daskals/Soil-Moisture-Scatter-Radio-Networking-with-Low-Power/Sensor Node-Tag/Version_Relative_Humidity/Kabianaki_TwoLayer/regulated_sensorTHV18.brd

## EAGLE design Sensor Node-Tag/Version_Relative_Humidity/Kabianaki_TwoLayer/regulated_sensorTHV18.brd (2017-01-12)

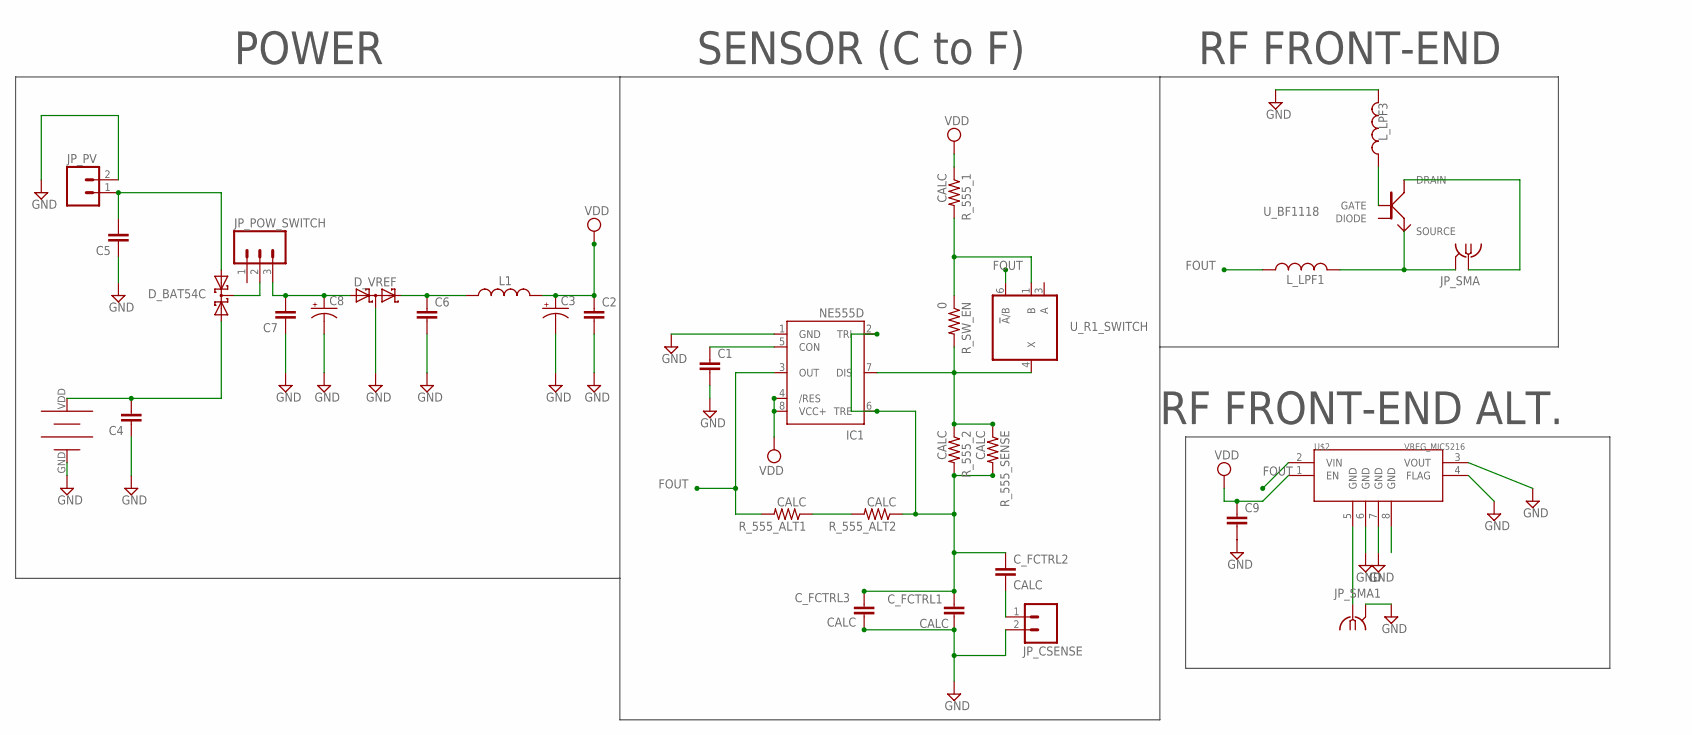
[picture p13: schematic regulated_sensorTHV18.sch]

Parts:
C1, C2, C4, C5, C6, C7, C9: CAP0603-CAP; 0603-CAP
C3, C8: CAP_POL1206; EIA3216
C_FCTRL1, C_FCTRL2, C_FCTRL3: CALC; 0603-CAP
D_BAT54C: BAT54C; SOT23
D_VREF: BAT54S; SOT23
IC1: NE555D; SO08
JP_CSENSE: M02LOCK; 1X02_LOCK
JP_POW_SWITCH: M03LOCK; 1X03_LOCK
JP_PV: M02LOCK; 1X02_LOCK
JP_SMA, JP_SMA1: SMA-142-0701-881/886; J502-ND-142-0701-881/886
L1: INDUCTOR0603; 0603
L_LPF1, L_LPF3: INDUCTOR0603; 0603
R_555_1: CALC; 0805
R_555_2, R_555_ALT1, R_555_ALT2, R_555_SENSE: CALC; 0603-RES
R_SW_EN: 0; 0805
U$1: BATTERY_AAA_EAGLE_PLASTIC_DEVICES_DOUBLE; BATTERY-AAA-50MM-DOUBLE
U$2: VREG_MIC5216; MSOP8
U_BF1118: BF1118SOT343R_NXP; SOT343R
U_R1_SWITCH: 741G3157DCKR; DCK_R-PDSO-G6

Connections:
FOUT: IC1.3 (OUT), L_LPF1.1, R_555_ALT1.2, U$2.2 (VIN), U_R1_SWITCH.6 (!A!/B)
GND: C1.2, C2.2, C3.C (-), C4.1, C5.1, C6.2, C7.1, C8.C (-), C9.2, C_FCTRL1.2, C_FCTRL3.2, D_VREF.3 (C1A2), IC1.1 (GND), JP_CSENSE.2, JP_PV.2, JP_SMA1.G@1 (2), JP_SMA1.G@2 (2), JP_SMA1.G@3 (2), JP_SMA1.G@4 (2), L_LPF3.2, U$1.GND, U$2.3 (VOUT), U$2.4 (FLAG), U$2.6 (GND), U$2.7 (GND), U_R1_SWITCH.2 (GND)
unnamed: C5.2, D_BAT54C.1 (A1), JP_PV.1
unnamed: C7.2, C8.A (+), D_VREF.1 (A1), JP_POW_SWITCH.3
unnamed: D_BAT54C.3 (CC), JP_POW_SWITCH.2
unnamed: L_LPF3.1, U_BF1118.1 (GATE)
unnamed: C6.1, D_VREF.2 (C2), L1.1
unnamed: C_FCTRL1.1, C_FCTRL2.1, C_FCTRL3.1, IC1.2 (TRI), IC1.6 (TRE), R_555_2.2, R_555_ALT2.1, R_555_SENSE.2
unnamed: C_FCTRL2.2, JP_CSENSE.1
unnamed: R_555_1.2, R_SW_EN.1, U_R1_SWITCH.1 (B)
unnamed: C1.1, IC1.5 (CON)
unnamed: IC1.7 (DIS), R_555_2.1, R_555_SENSE.1, R_SW_EN.2, U_R1_SWITCH.4 (X)
unnamed: JP_SMA1.1, U$2.5 (GND)
unnamed: C4.2, D_BAT54C.2 (A2), U$1.VDD
unnamed: R_555_ALT1.1, R_555_ALT2.2
RF_FEEDBACK: JP_SMA.G@1 (2), JP_SMA.G@2 (2), JP_SMA.G@3 (2), JP_SMA.G@4 (2), L_LPF1.2, U_BF1118.3 (SOURCE)
RF_IN: JP_SMA.1, U_BF1118.4 (DRAIN)
VDD: C2.1, C3.A (+), C9.1, IC1.4 (/RES), IC1.8 (VCC+), L1.2, R_555_1.1, U$2.1 (EN), U_R1_SWITCH.5 (VCC)

Notes on the sheet:
POWER
SENSOR (C to F)
RF FRONT-END
RF FRONT-END ALT.

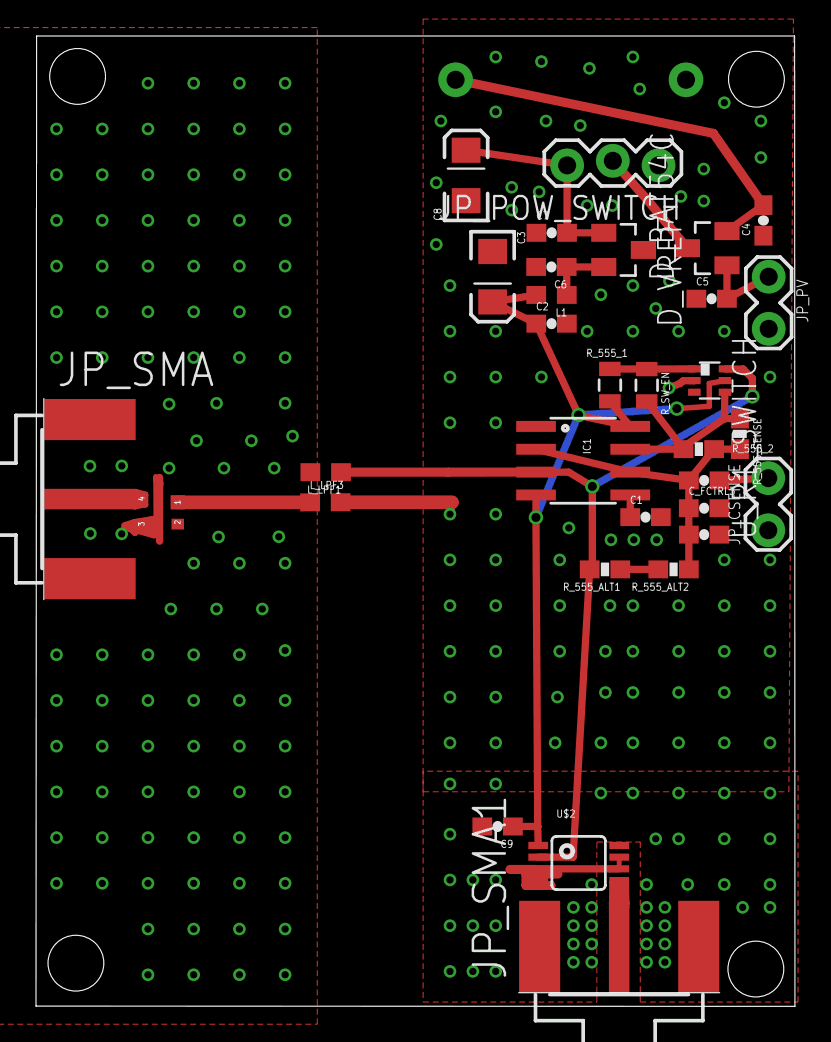
[picture p14: board regulated_sensorTHV18.brd from above]

Board: 2 copper layers, 42.2 x 53.9 mm, 33 parts (1 on the bottom side), 18 nets.
